shortlurker/LCK75/LCK75 Images/LCK75_SL_back_components.png

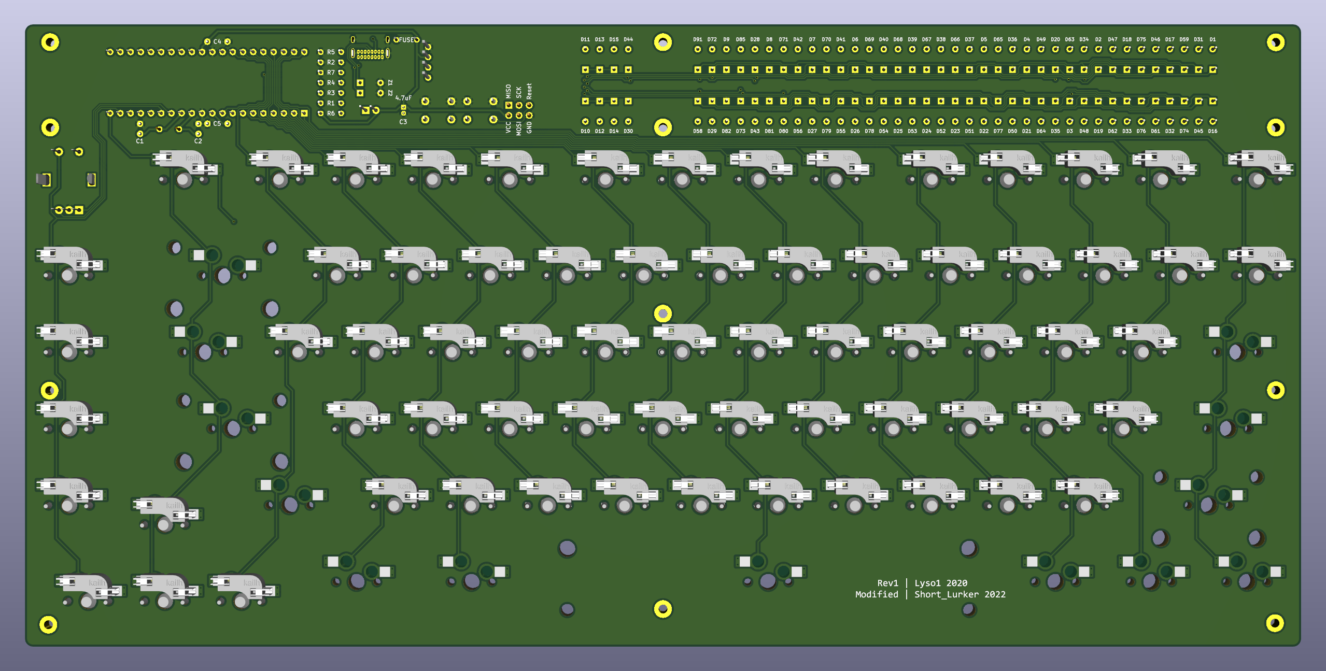
LCK75 Images/LCK75_SL_back_components.png
