shortlurker/LCK75/LCK75 Images/LCK75_SL_front_components.png

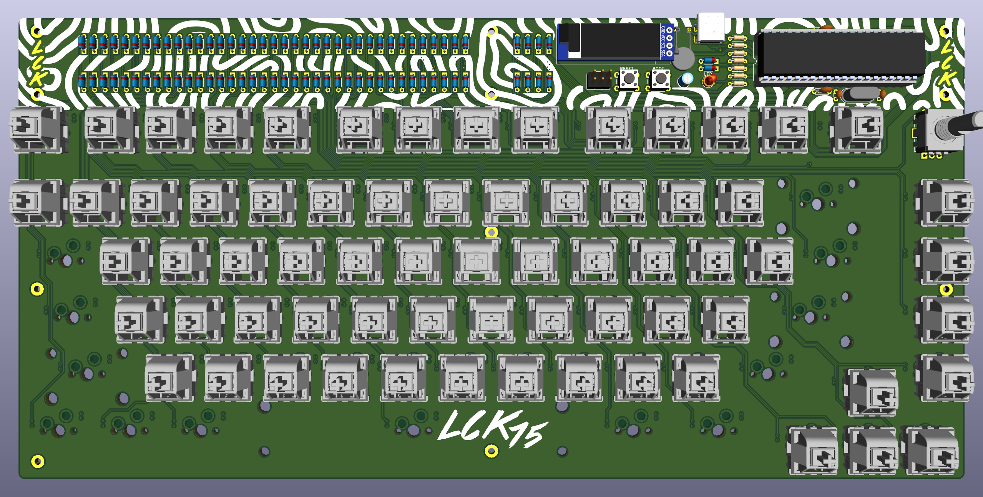
LCK75 Images/LCK75_SL_front_components.png
